kowals14/microphone-interface/Final/AudioFX/audioFX.c

/*
 * audioFX.c
 *
 *  Created on: Mar 20, 2024
 *      Author: Jakub Kowalski
 */
#include "audioFX.h"
#include "filters.h"
#include "delay.h"
#include "distort.h"

extern int16_t* p_in_buff;
extern int16_t* p_out_buff;

extern FILTERS_Params f_p0;
extern FILTERS_Params f_p1;
extern FILTERS_Params f_p2;
extern FILTERS_Params f_p3;
extern FILTERS_Params f_p4;

extern DELAY_Params 	dl_p;
extern DISTORT_Params 	ds_p;

extern AUDIOFX_Type curr_fx;

extern uint8_t 	update_flags;
extern uint16_t timer_count[3];

void AUDIOFX_UpdateCounters() {
	// convert the current fx parameters to corresponding timer values
	switch(curr_fx) {
		case AUDIOFX_FILTER0:
				{
					TIM1->CNT = PARAM_TO_CNTR(FILTERS_MAX_FREQ, FILTERS_MIN_FREQ,	f_p0.f0);
					TIM3->CNT = PARAM_TO_CNTR(FILTERS_MAX_BW, 	FILTERS_MIN_BW, 	f_p0.BW);
					TIM4->CNT = PARAM_TO_CNTR(FILTERS_MAX_G, 	FILTERS_MIN_G, 		f_p0.G);
					break;
				}
		case AUDIOFX_FILTER1:
				{
					TIM1->CNT = PARAM_TO_CNTR(FILTERS_MAX_FREQ, FILTERS_MIN_FREQ, 	f_p1.f0);
					TIM3->CNT = PARAM_TO_CNTR(FILTERS_MAX_BW, 	FILTERS_MIN_BW, 	f_p1.BW);
					TIM4->CNT = PARAM_TO_CNTR(FILTERS_MAX_G, 	FILTERS_MIN_G, 		f_p1.G);
					break;
				}
		case AUDIOFX_FILTER2:
				{
					TIM1->CNT = PARAM_TO_CNTR(FILTERS_MAX_FREQ, FILTERS_MIN_FREQ, 	f_p2.f0);
					TIM3->CNT = PARAM_TO_CNTR(FILTERS_MAX_BW, 	FILTERS_MIN_BW, 	f_p2.BW);
					TIM4->CNT = PARAM_TO_CNTR(FILTERS_MAX_G, 	FILTERS_MIN_G, 		f_p2.G);
					break;
				}
		case AUDIOFX_FILTER3:
				{
					TIM1->CNT = PARAM_TO_CNTR(FILTERS_MAX_FREQ, FILTERS_MIN_FREQ, 	f_p3.f0);
					TIM3->CNT = PARAM_TO_CNTR(FILTERS_MAX_BW, 	FILTERS_MIN_BW, 	f_p3.BW);
					TIM4->CNT = PARAM_TO_CNTR(FILTERS_MAX_G, 	FILTERS_MIN_G, 		f_p3.G);
					break;
				}
		case AUDIOFX_FILTER4:
				{
					TIM1->CNT = PARAM_TO_CNTR(FILTERS_MAX_FREQ, FILTERS_MIN_FREQ, 	f_p4.f0);
					TIM3->CNT = PARAM_TO_CNTR(FILTERS_MAX_BW, 	FILTERS_MIN_BW,		f_p4.BW);
					TIM4->CNT = PARAM_TO_CNTR(FILTERS_MAX_G, 	FILTERS_MIN_G, 		f_p4.G);
					break;
				}
		case AUDIOFX_DELAY:
				{
					TIM1->CNT = PARAM_TO_CNTR(DELAY_MAX_MIX,		DELAY_MIN_MIX,		dl_p.mix);	// mix
					TIM3->CNT = PARAM_TO_CNTR(DELAY_MAX_FEEDBACK,	DELAY_MIN_FEEDBACK,	dl_p.feedback);	// feedback
					TIM4->CNT = PARAM_TO_CNTR(DELAY_MAX_TIME_MS,	DELAY_MIN_TIME_MS,	dl_p.time_ms);	// delay time
					break;
				}
		case AUDIOFX_DISTORTION:
				{
					TIM1->CNT = PARAM_TO_CNTR(DISTORT_MAX_PREAMP, 	DISTORT_MIN_PREAMP, ds_p.pre_amp);
					TIM3->CNT = PARAM_TO_CNTR(DISTORT_MAX_MIX, 		DISTORT_MIN_MIX, 	ds_p.mix);
					TIM4->CNT = PARAM_TO_CNTR(DISTORT_MAX_GAIN, 	DISTORT_MIN_GAIN, 	ds_p.gain);
					break;
				}
	}

	timer_count[0] = TIM1->CNT;
	timer_count[1] = TIM3->CNT;
	timer_count[2] = TIM4->CNT;
}

/**
 * Switch the current FX to be controlled
 */
void AUDIOFX_SwitchFX(uint8_t dir) {
	if(dir) {
		curr_fx++;
	}
	else {
		curr_fx--;
	}

	if(curr_fx == AUDIOFX_MAX_CHAIN) {
		curr_fx = 0;
	}
	else if(curr_fx == -1) {
		curr_fx = AUDIOFX_MAX_CHAIN - 1;
	}

	AUDIOFX_UpdateCounters();
}

void AUDIOFX_SetParams(AUDIOFX_Type fx) {
	// set the new parameters as temporary and set the update flag for the corresponding effect

	switch (fx)
	{
		case AUDIOFX_DELAY:
		{
			dl_p.temp[0] = CNTR_TO_PARAM(DELAY_MAX_MIX,			DELAY_MIN_MIX,		(timer_count[0]));	// mix
			dl_p.temp[1] = CNTR_TO_PARAM(DELAY_MAX_FEEDBACK,	DELAY_MIN_FEEDBACK,	(timer_count[1]));	// feedback
			dl_p.temp[2] = CNTR_TO_PARAM(DELAY_MAX_TIME_MS,		DELAY_MIN_TIME_MS,	(timer_count[2]));	// delay time
//
			update_flags |= UPDATE_DELAY;

			break;
		}
		case AUDIOFX_DISTORTION:
		{
			ds_p.temp[0] = CNTR_TO_PARAM(DISTORT_MAX_PREAMP,	DISTORT_MIN_PREAMP,	(timer_count[0]));	// pre amp
			ds_p.temp[1] = CNTR_TO_PARAM(DISTORT_MAX_MIX,		DISTORT_MIN_MIX,	(timer_count[1]));	// mix
			ds_p.temp[2] = CNTR_TO_PARAM(DISTORT_MAX_GAIN,		DISTORT_MIN_GAIN,	(timer_count[2]));	// gain

			update_flags |= UPDATE_DISTORT;

			break;
		}
		case AUDIOFX_FILTER0:
		{

			f_p0.temp[0] = CNTR_TO_PARAM(FILTERS_MAX_FREQ,	FILTERS_MIN_FREQ,	(timer_count[0]));	// center frequency
			f_p0.temp[1] = CNTR_TO_PARAM(FILTERS_MAX_BW,	FILTERS_MIN_BW,		(timer_count[1]));						// bandwidth
			f_p0.temp[2] = CNTR_TO_PARAM(FILTERS_MAX_G,		FILTERS_MIN_G,		(timer_count[2]));	// boost/cut

			update_flags |= UPDATE_FILTER0;

			break;
		}
		case AUDIOFX_FILTER1:
		{

			f_p1.temp[0] = CNTR_TO_PARAM(FILTERS_MAX_FREQ,	FILTERS_MIN_FREQ,	(timer_count[0]));	// center frequency
			f_p1.temp[1] = CNTR_TO_PARAM(FILTERS_MAX_BW,	FILTERS_MIN_BW,		(timer_count[1]));						// bandwidth
			f_p1.temp[2] = CNTR_TO_PARAM(FILTERS_MAX_G,		FILTERS_MIN_G,		(timer_count[2]));	// boost/cut

			update_flags |= UPDATE_FILTER1;

			break;
		}
		case AUDIOFX_FILTER2:
		{

			f_p2.temp[0] = CNTR_TO_PARAM(FILTERS_MAX_FREQ,	FILTERS_MIN_FREQ,	(timer_count[0]));	// center frequency
			f_p2.temp[1] = CNTR_TO_PARAM(FILTERS_MAX_BW,	FILTERS_MIN_BW,		(timer_count[1]));	// bandwidth
			f_p2.temp[2] = CNTR_TO_PARAM(FILTERS_MAX_G,		FILTERS_MIN_G,		(timer_count[2]));	// boost/cut

			update_flags |= UPDATE_FILTER2;

			break;
		}
		case AUDIOFX_FILTER3:
		{

			f_p3.temp[0] = CNTR_TO_PARAM(FILTERS_MAX_FREQ,	FILTERS_MIN_FREQ,	(timer_count[0]));	// center frequency
			f_p3.temp[1] = CNTR_TO_PARAM(FILTERS_MAX_BW,	FILTERS_MIN_BW,		(timer_count[1]));	// bandwidth
			f_p3.temp[2] = CNTR_TO_PARAM(FILTERS_MAX_G,		FILTERS_MIN_G,		(timer_count[2]));	// boost/cut

			update_flags |= UPDATE_FILTER3;

			break;
		}
		case AUDIOFX_FILTER4:
		{

			f_p4.temp[0] = CNTR_TO_PARAM(FILTERS_MAX_FREQ,	FILTERS_MIN_FREQ,	(timer_count[0]));	// center frequency
			f_p4.temp[1] = CNTR_TO_PARAM(FILTERS_MAX_BW,	FILTERS_MIN_BW,		(timer_count[1]));	// bandwidth
			f_p4.temp[2] = CNTR_TO_PARAM(FILTERS_MAX_G,		FILTERS_MIN_G,		(timer_count[2]));	// boost/cut

			update_flags |= UPDATE_FILTER4;

			break;
		}
	}
}

void AUDIOFX_Apply_FX_Chain(void) {
	float left_in;
	float right_in;

	int16_t left_out;
	int16_t right_out;

	if(update_flags) {
		// check the update flags
		if(update_flags & UPDATE_DELAY) {
			DELAY_SetParams(&dl_p, dl_p.temp[0], dl_p.temp[1], dl_p.temp[2]);
		}
		if(update_flags & UPDATE_DISTORT) {
			DISTORT_SetParams(&ds_p, ds_p.temp[0], ds_p.temp[1], ds_p.temp[2]);
		}
		if(update_flags & UPDATE_FILTER0) {
			FILTERS_SetParams_PKNG(&f_p0, f_p0.temp[0], f_p0.temp[1], f_p0.temp[2]);
		}
		if(update_flags & UPDATE_FILTER1) {
			FILTERS_SetParams_PKNG(&f_p1, f_p1.temp[0], f_p1.temp[1], f_p1.temp[2]);
		}
		if(update_flags & UPDATE_FILTER2) {
			FILTERS_SetParams_PKNG(&f_p2, f_p2.temp[0], f_p2.temp[1], f_p2.temp[2]);
		}
		if(update_flags & UPDATE_FILTER3) {
			FILTERS_SetParams_PKNG(&f_p3, f_p3.temp[0], f_p3.temp[1], f_p3.temp[2]);
		}
		if(update_flags & UPDATE_FILTER4) {
			FILTERS_SetParams_PKNG(&f_p4, f_p4.temp[0], f_p4.temp[1], f_p4.temp[2]);
		}

		// clear the flags
		update_flags = 0;
	}

	for(uint8_t n = 0; n < (AUDIOFX_BUFF_SIZE/2) - 1; n += 2) {
		left_in		= INT16_TO_FLOAT * ((float) p_in_buff[n]);
		right_in	= INT16_TO_FLOAT * ((float) p_in_buff[n + 1]);

		left_in		= DISTORT_Apply(left_in, &ds_p);
		right_in 	= DISTORT_Apply(right_in, &ds_p);

		left_in		= FILTERS_Apply(left_in, &f_p0);
		right_in 	= FILTERS_Apply(right_in, &f_p0);

		left_in		= FILTERS_Apply(left_in, &f_p1);
		right_in 	= FILTERS_Apply(right_in, &f_p1);

		left_in		= FILTERS_Apply(left_in, &f_p2);
		right_in 	= FILTERS_Apply(right_in, &f_p2);

		left_in		= FILTERS_Apply(left_in, &f_p3);
		right_in 	= FILTERS_Apply(right_in, &f_p3);

		left_in		= FILTERS_Apply(left_in, &f_p4);
		right_in 	= FILTERS_Apply(right_in, &f_p4);

		left_in		= DELAY_Apply(left_in, &dl_p);
		right_in 	= DELAY_Apply(right_in, &dl_p);

		left_out	= (int16_t) (FLOAT_TO_INT16 * left_in);
		right_out 	= (int16_t) (FLOAT_TO_INT16 * right_in);

		p_out_buff[n] 		= left_out;
		p_out_buff[n + 1] 	= right_out;
	}
}
